MagicSmokeBlog/Philips-PM2535-Kermit/Software/PM25XX_OLED/PM25XX_OLED.h

#ifndef PM25XX_OLED_DISPLAY_PM25XX_OLED_H
#define PM25XX_OLED_DISPLAY_PM25XX_OLED_H

/**
 * Debugging mode. Define as 1 for development and as 0 for production.
 */
#define DEBUG 0

#endif //PM25XX_OLED_DISPLAY_PM25XX_OLED_H
